oldgerman/STM32-DEV-BRD/F4x1_Dev/F4x1_Dev_Project/Datasheets/W25Q32-Large-Capacity-FLASH-Storage-Module-SPI-Interface-600x600.jpg

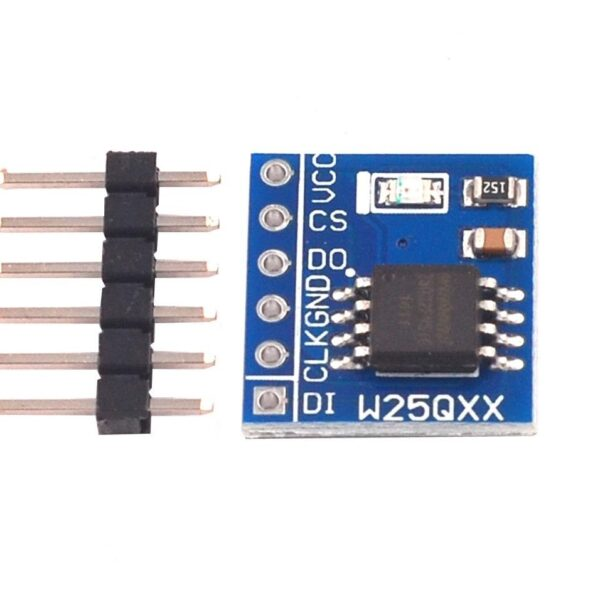
F4x1_Dev/F4x1_Dev_Project/Datasheets/W25Q32-Large-Capacity-FLASH-Storage-Module-SPI-Interface-600x600.jpg
