oldgerman/STM32-DEV-BRD/G031_Dev/G031_Dev_Project/Images/Top_2Dview.png

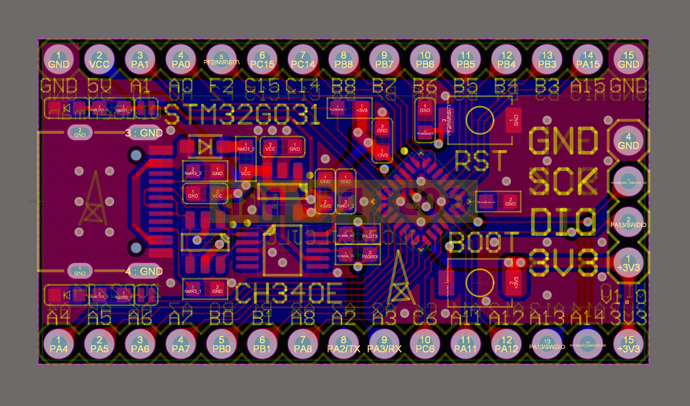
G031_Dev/G031_Dev_Project/Images/Top_2Dview.png
