oldgerman/STM32-DEV-BRD/G031_Dev/G031_Dev_Project/Images/Top_3Dview_NP.png

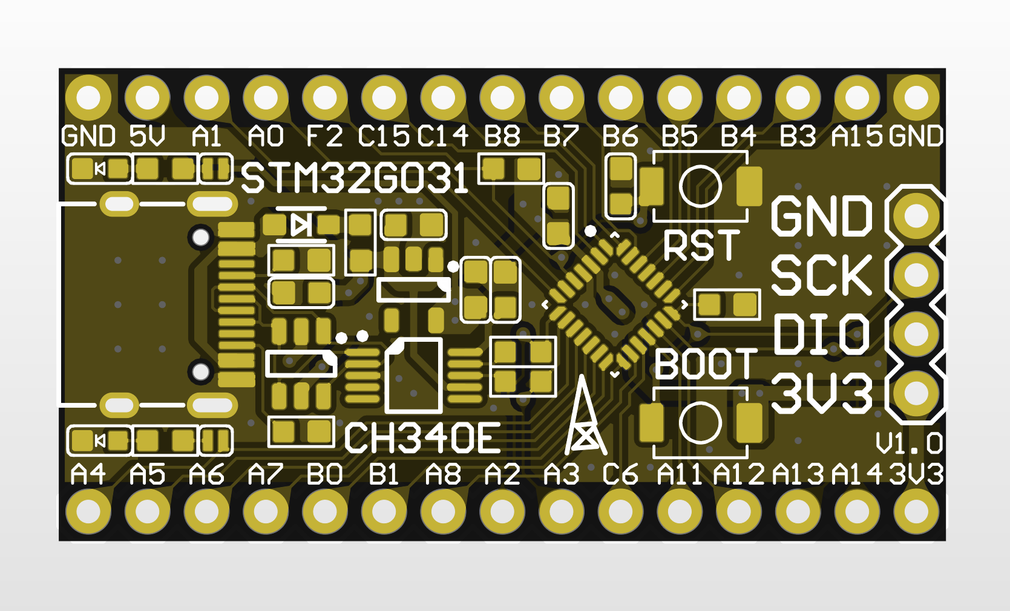
G031_Dev/G031_Dev_Project/Images/Top_3Dview_NP.png
