oldgerman/STM32-DEV-BRD/G431_Dev/G431_Dev_Project/20240229_Altium/Images/20240229_3D.png

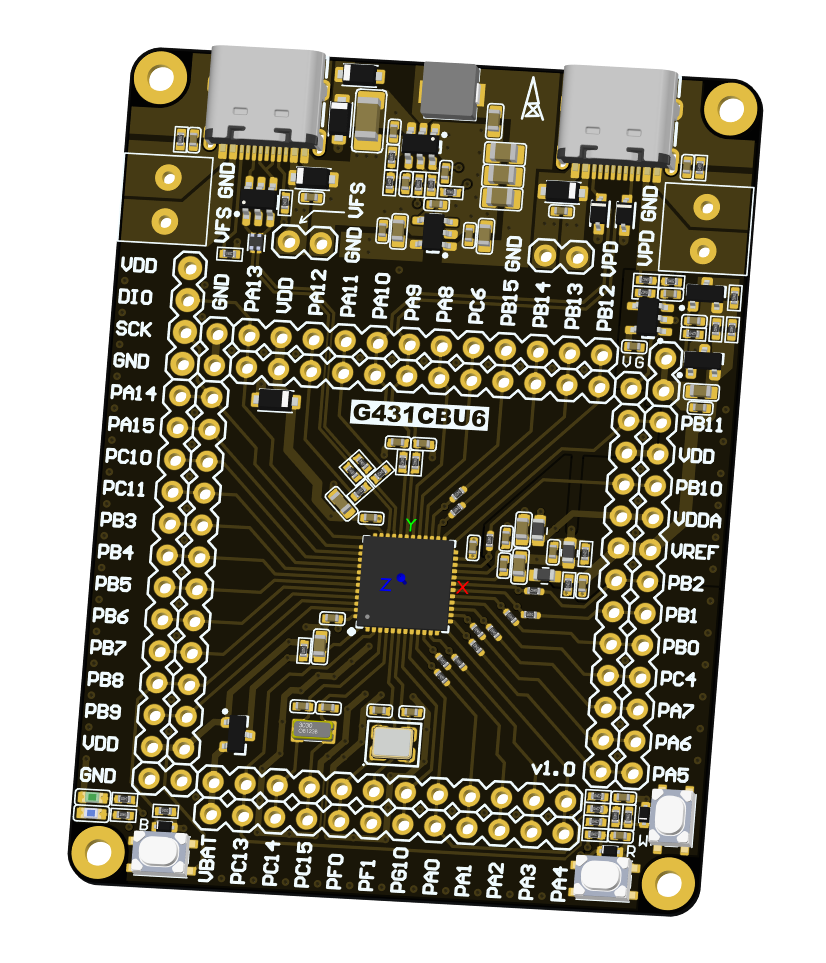
G431_Dev/G431_Dev_Project/20240229_Altium/Images/20240229_3D.png
