oldgerman/STM32-DEV-BRD/G431_Dev/G431_Dev_Project/20240229_Altium/Images/JLC_USB2.0阻抗.png

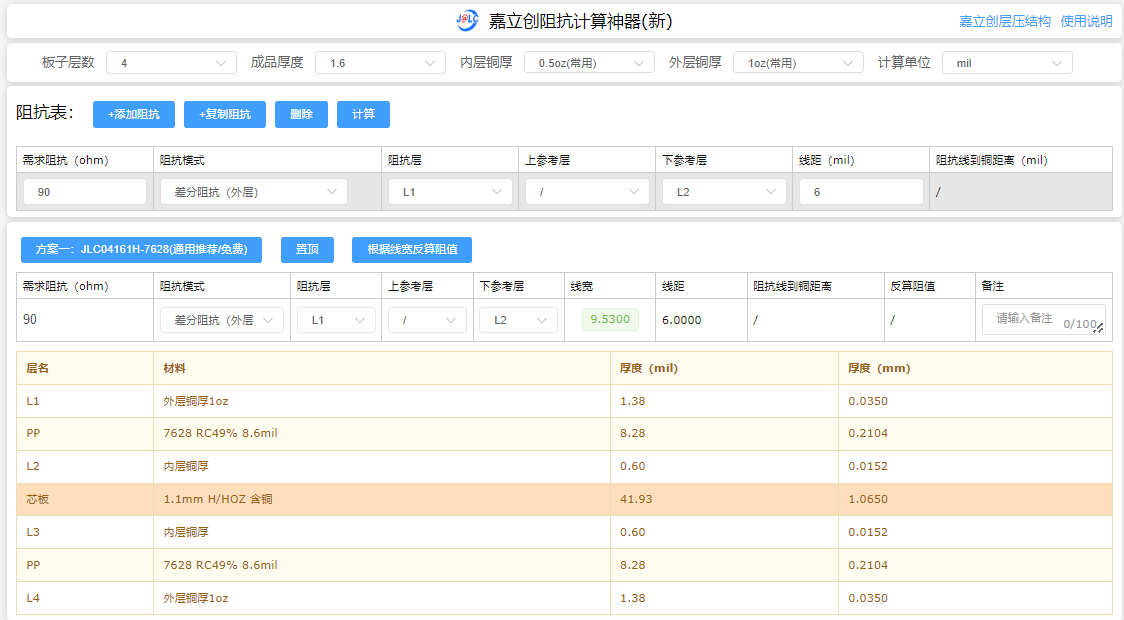
G431_Dev/G431_Dev_Project/20240229_Altium/Images/JLC_USB2.0阻抗.png
