oldgerman/STM32-DEV-BRD/Images/F4x1_DEV_BRD(2).jpeg

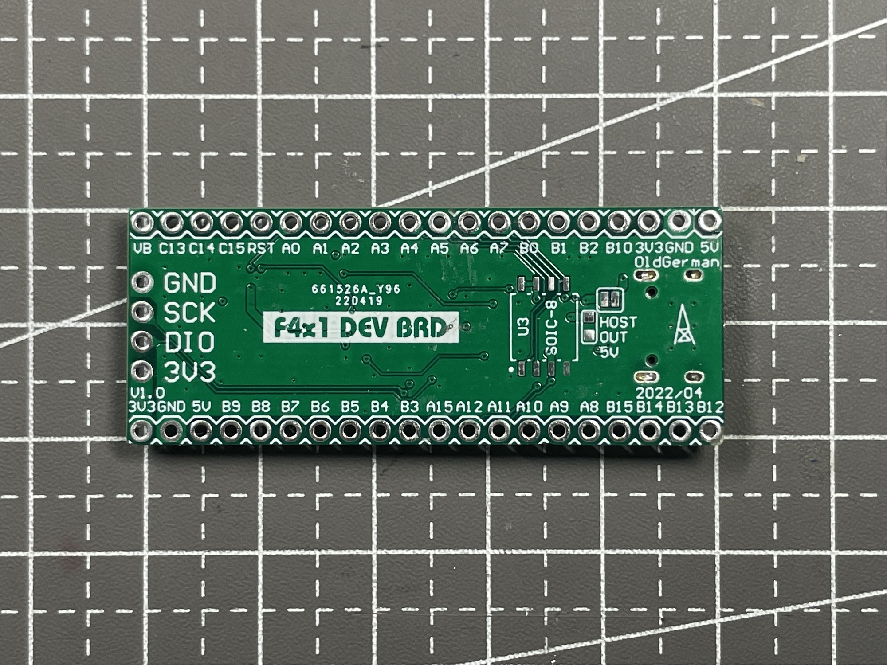
Images/F4x1_DEV_BRD(2).jpeg
