oldgerman/STM32-DEV-BRD/Images/mix(2).jpeg

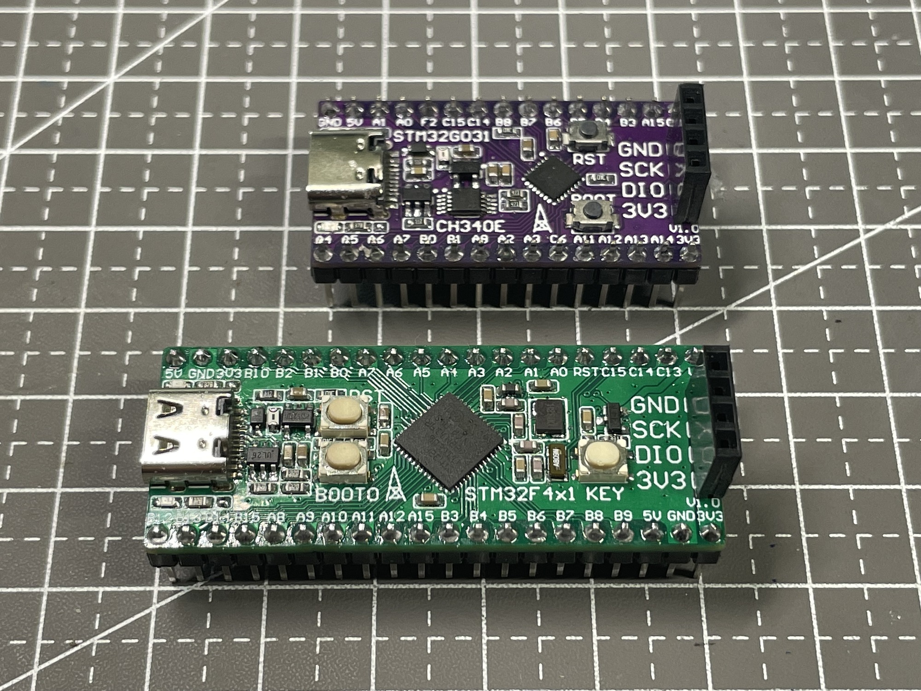
Images/mix(2).jpeg
