oldgerman/STM32-DEV-BRD/G031_Dev/STM32G031G8Ux最小系统板串口测试程序/G031G8U6_DEV_BRD/SYSTEM/usart/usart.c

#include "usart.h"

#if EN_USART1_RX

uint8_t USART_RX_BUF[USART_REC_LEN];
uint16_t USART_RX_STA=0;

uint8_t aRxBuffer[RXBUFFERSIZE];//HAL搴撲娇鐢ㄧ殑涓插彛鎺ユ敹缂撳啿

//重定义fputc函数
int fputc(int ch, FILE *f)
{
	while((USART2->ISR&0X40)==0);//循环发送,直到发送完毕
    USART2->RDR = (uint8_t) ch;
	return ch;
}

//涓柇鍥炶皟鍑芥暟
void HAL_UART_RxCpltCallback(UART_HandleTypeDef *huart)
{
	if(huart->Instance==USART2)
	{
		if((USART_RX_STA&0x8000)==0)
		{

			if(USART_RX_STA&0x4000)
			{
				if(aRxBuffer[0]!=0x0a)
					USART_RX_STA=0;
				else
					USART_RX_STA|=0x8000;
			}
			else //杩樻病鏀跺埌0X0D
			{
				if(aRxBuffer[0]==0x0d)USART_RX_STA|=0x4000;
				else
				{
					USART_RX_BUF[USART_RX_STA&0X3FFF]=aRxBuffer[0] ;
					USART_RX_STA++;
					if(USART_RX_STA>(USART_REC_LEN-1))
						USART_RX_STA=0;
				}
			}
		}
	}
}

#endif


PUTCHAR_PROTOTYPE
{

	HAL_UART_Transmit(&huart2, (uint8_t *)&ch, 1 , 0xffff);
	return ch;
}
