oldgerman/STM32-DEV-BRD/G031_Dev/STM32G031G8Ux最小系统板串口测试程序/G031G8U6_DEV_BRD/SYSTEM/usart/usart.h

#ifndef __USART_H
#define __USART_H
#include "main.h"

#include "stdio.h"//寰楀厛鍖呭惈

#ifdef __GNUC__
#define PUTCHAR_PROTOTYPE int __io_putchar(int ch)
#else
#define PUTCHAR_PROTOTYPE int fputc(int ch, FILE *f)
#endif

// 浠ヤ笅涓哄師瀛愮殑
#define USART_REC_LEN  			200
#define EN_USART1_RX 			1

extern uint8_t  USART_RX_BUF[USART_REC_LEN];
extern uint16_t USART_RX_STA;
extern UART_HandleTypeDef UART1_Handler; 	//UART鍙ユ焺

#define RXBUFFERSIZE   1 					//缂撳瓨澶у皬
extern uint8_t aRxBuffer[RXBUFFERSIZE];			//HAL搴揢SART鎺ユ敹Buffer

void uart_init(uint32_t bound);


extern UART_HandleTypeDef huart2;
#endif
